dhir08/ankl-prosthetic-ankle/electrical/kicad/ANKL-electrical_wiring.kicad_sch

## KiCad design electrical/kicad/ANKL-electrical_wiring.kicad_sch (2026-08-11)

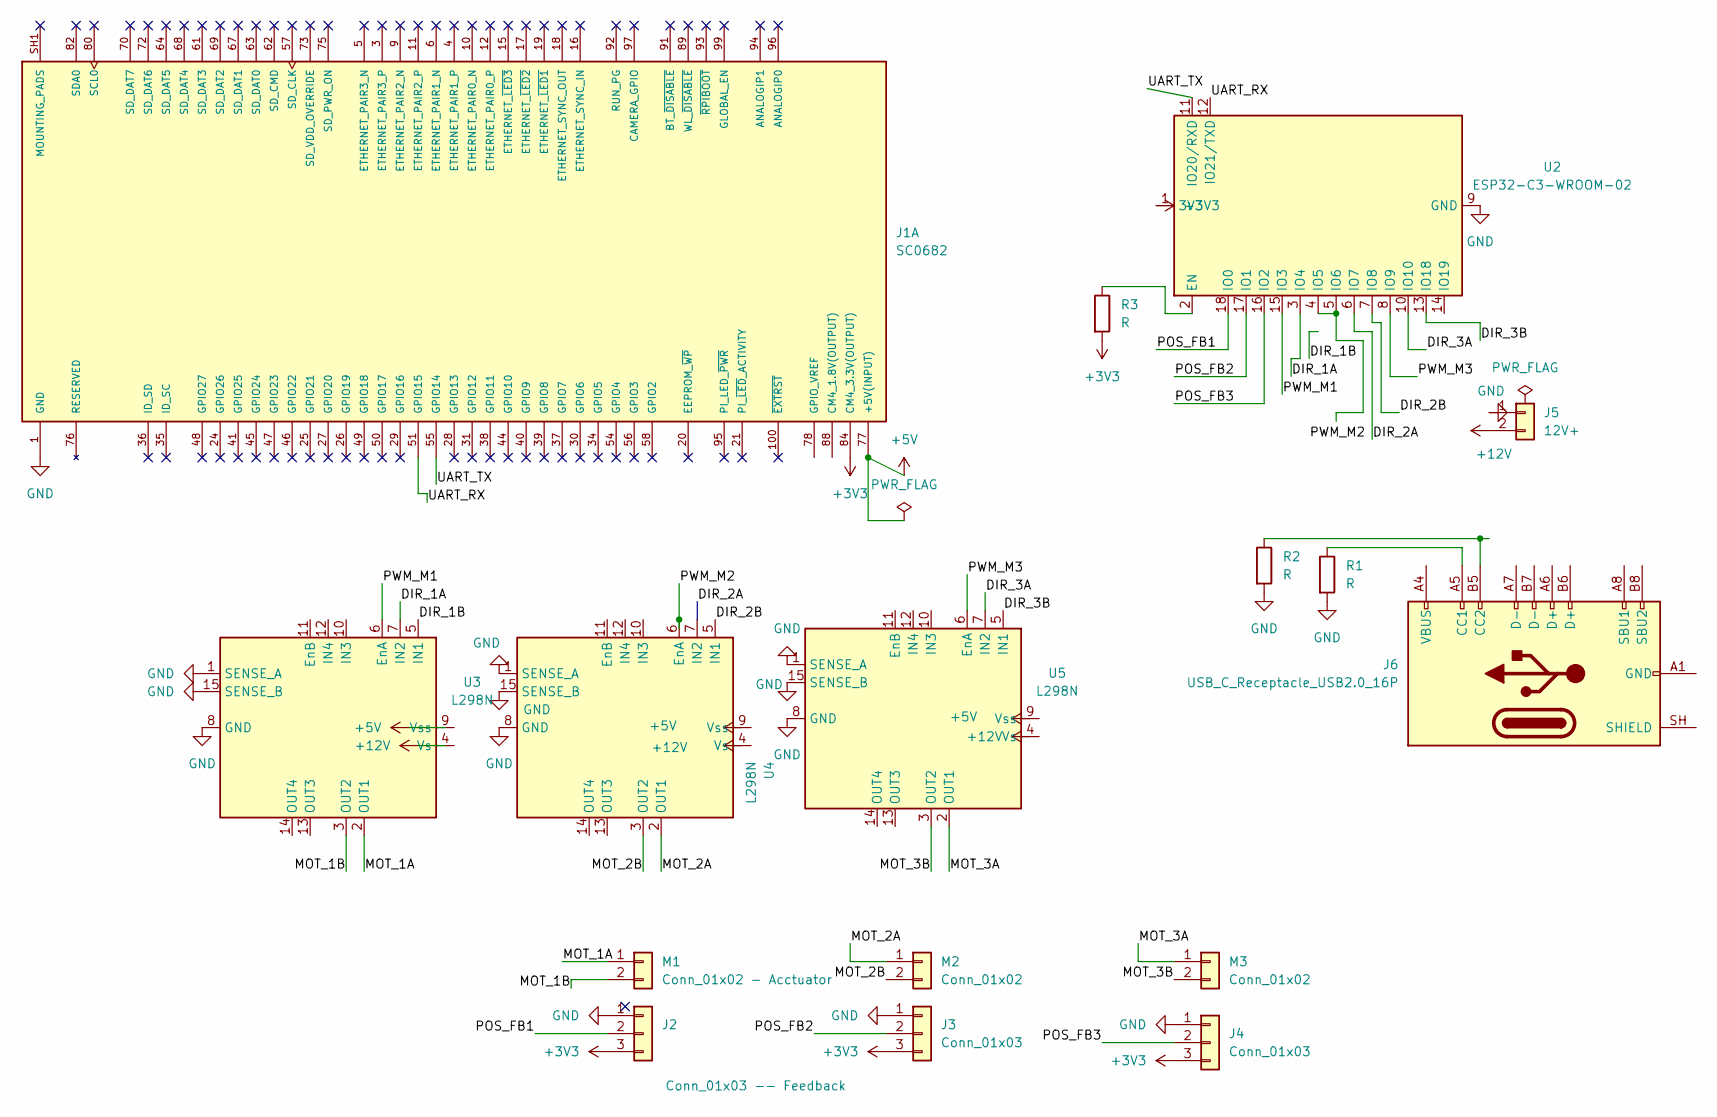
[picture p16: schematic ANKL-electrical_wiring.kicad_sch]

Parts:
J1: SC0682; MODULE_SC0682; PARTREV 2021-10-12; DigiKey_Part_Number 2648-SC0682-ND
J2: Conn_01x03 -- Feedback
J3, J4: Conn_01x03
J5: 12V+
J6: USB_C_Receptacle_USB2.0_16P
M1: Conn_01x02 - Acctuator
M2, M3: Conn_01x02
R1, R2, R3: R
U2: ESP32-C3-WROOM-02
U3, U4, U5: L298N; TO-220-15_P2.54x5.08mm_StaggerOdd_Lead4.58mm_Vertical

Connections:
+3V3: J1.84 (CM4_3.3V(OUTPUT)), J1.86 (CM4_3.3V(OUTPUT)), J2.3, J3.3, J4.3, R3.2, U2.1 (3V3)
+5V: J1.77 (+5V(INPUT)), J1.79 (+5V(INPUT)), J1.81 (+5V(INPUT)), J1.83 (+5V(INPUT)), J1.85 (+5V(INPUT)), J1.87 (+5V(INPUT))
+12V: J5.2
DIR_1A: U2.3 (IO4), U3.7 (IN2)
DIR_1B: U3.5 (IN1)
DIR_2A: U2.6 (IO7)
DIR_2B: U2.7 (IO8), U4.5 (IN1)
DIR_3A: U2.10 (IO10), U5.7 (IN2)
DIR_3B: U2.13 (IO18), U5.5 (IN1)
GND: J1.1 (GND), J1.2 (GND), J1.7 (GND), J1.8 (GND), J1.13 (GND), J1.14 (GND), J1.22 (GND), J1.23 (GND), J1.32 (GND), J1.33 (GND), J1.42 (GND), J1.43 (GND), J1.52 (GND), J1.53 (GND), J1.59 (GND), J1.60 (GND), J1.65 (GND), J1.66 (GND), J1.71 (GND), J1.74 (GND), J1.98 (GND), J1.107 (GND), J1.108 (GND), J1.113 (GND), J1.114 (GND), J1.119 (GND), J1.120 (GND), J1.125 (GND), J1.126 (GND), J1.131 (GND), J1.132 (GND), J1.137 (GND), J1.138 (GND), J1.144 (GND), J1.150 (GND), J1.155 (GND), J1.156 (GND), J1.161 (GND), J1.162 (GND), J1.167 (GND), J1.168 (GND), J1.173 (GND), J1.174 (GND), J1.179 (GND), J1.180 (GND), J1.185 (GND), J1.186 (GND), J1.191 (GND), J1.192 (GND), J1.197 (GND), J1.198 (GND), J2.1, J3.1, J4.1, J5.1, R1.2, R2.2, U2.9 (GND), U2.19 (GND), U3.1 (SENSE_A), U3.8 (GND), U3.15 (SENSE_B), U4.1 (SENSE_A), U4.8 (GND), U4.15 (SENSE_B), U5.1 (SENSE_A), U5.8 (GND), U5.15 (SENSE_B)
MOT_1A: M1.1, U3.2 (OUT1)
MOT_1B: M1.2, U3.3 (OUT2)
MOT_2A: M2.1, U4.2 (OUT1)
MOT_2B: M2.2, U4.3 (OUT2)
MOT_3A: M3.1, U5.2 (OUT1)
MOT_3B: M3.2, U5.3 (OUT2)
unnamed: J1.88 (CM4_1.8V(OUTPUT)), J1.90 (CM4_1.8V(OUTPUT))
unnamed: J1.76 (RESERVED), J1.104 (RESERVED), J1.106 (RESERVED)
unnamed: J1.SH1 (MOUNTING_PADS), J1.SH2 (MOUNTING_PADS), J1.SH3 (MOUNTING_PADS), J1.SH4 (MOUNTING_PADS)
unnamed: J6.A1 (GND), J6.A12 (GND), J6.B1 (GND), J6.B12 (GND)
unnamed: J6.A4 (VBUS), J6.A9 (VBUS), J6.B4 (VBUS), J6.B9 (VBUS)
unnamed: J6.A5 (CC1), R1.1
unnamed: J6.B5 (CC2), R2.1
unnamed: R3.1, U2.2 (EN)
unnamed: U2.4 (IO5), U2.5 (IO6)
POS_FB1: J2.2, U2.18 (IO0)
POS_FB2: J3.2, U2.17 (IO1)
POS_FB3: J4.2, U2.16 (IO2)
PWM_M1: U2.15 (IO3), U3.6 (EnA)
PWM_M2: U4.6 (EnA)
PWM_M3: U2.8 (IO9), U5.6 (EnA)
UART_RX: J1.51 (GPIO15), U2.12 (IO21/TXD)
UART_TX: J1.55 (GPIO14), U2.11 (IO20/RXD)
